svenpetersen1965/C64_PSU_Z66/Rev. 1/pictures/1055_-_DIN-Plug_top.JPG

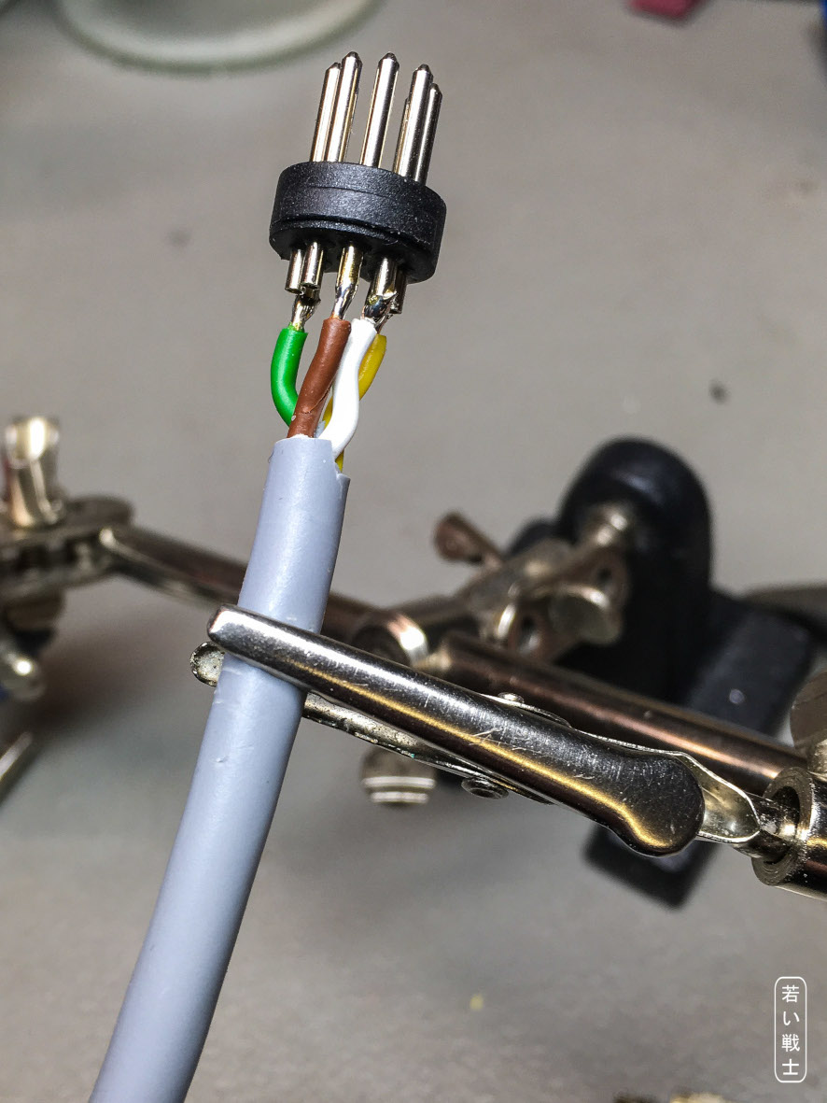
Rev. 1/pictures/1055_-_DIN-Plug_top.JPG
