svenpetersen1965/C64_PSU_Z66/Rev. 1/pictures/1056_-_DIN-Plug_bottom.JPG

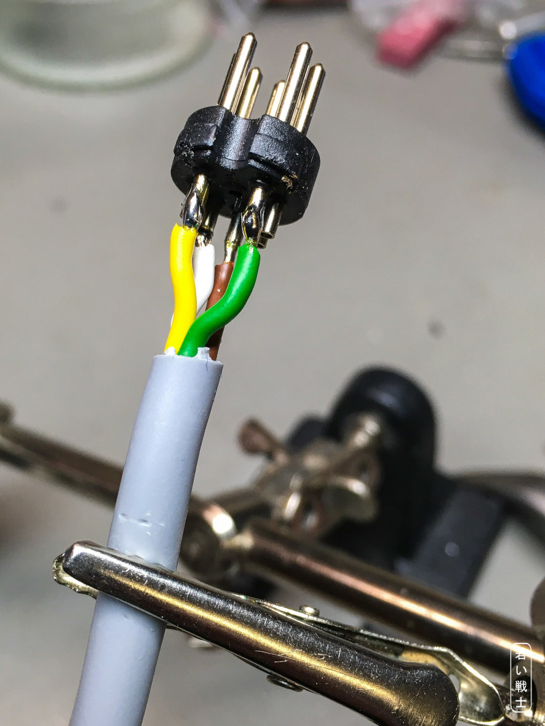
Rev. 1/pictures/1056_-_DIN-Plug_bottom.JPG
