svenpetersen1965/C64_PSU_Z66/Rev. 1/pictures/1057_-_Mains_Switch.JPG

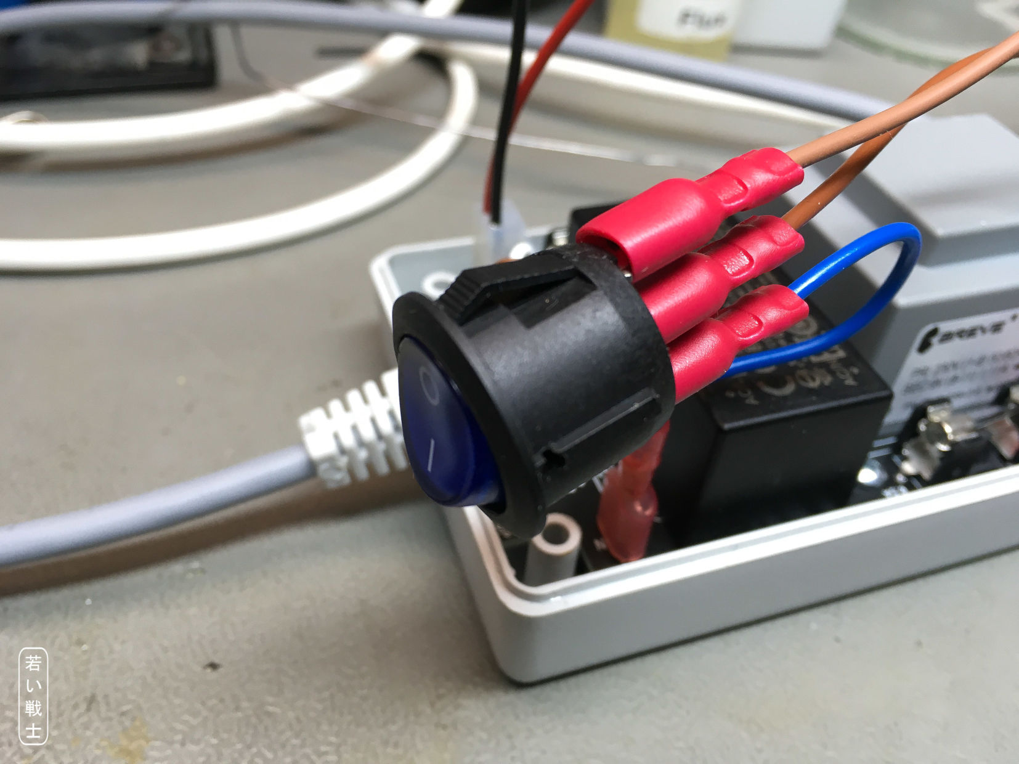
Rev. 1/pictures/1057_-_Mains_Switch.JPG
