svenpetersen1965/C64_PSU_Z66/Rev. 1/pictures/1165_-_thermal_el_load.JPG

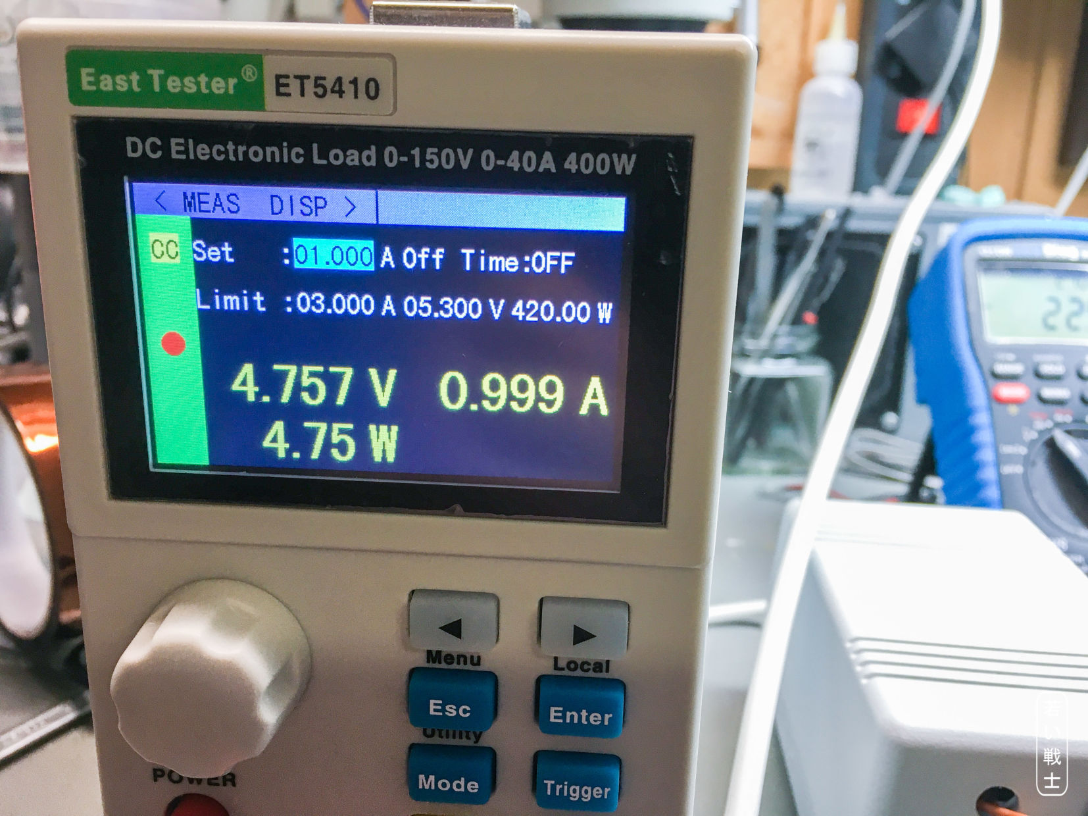
Rev. 1/pictures/1165_-_thermal_el_load.JPG
