svenpetersen1965/C64_PSU_Z66/Rev. 1/pictures/1166_-_thermal_load_resistors.JPG

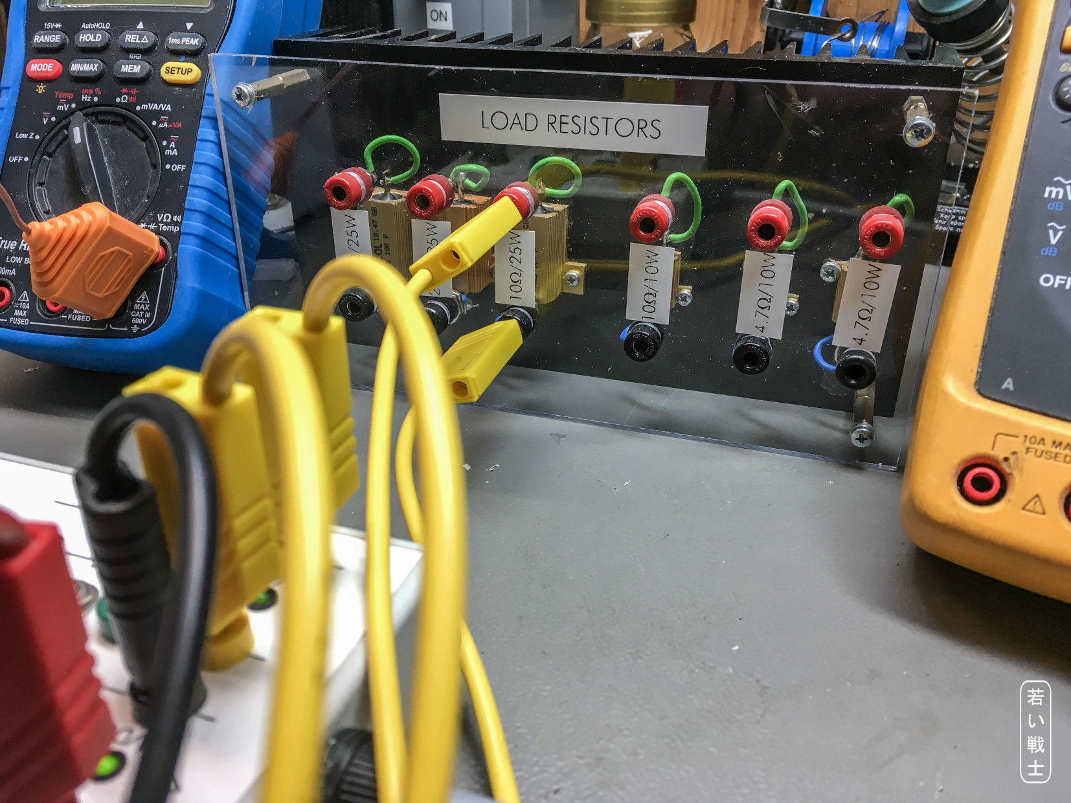
Rev. 1/pictures/1166_-_thermal_load_resistors.JPG
