svenpetersen1965/C64_PSU_Z66/Rev. 1/pictures/1183_-_thermal_final_config.JPG

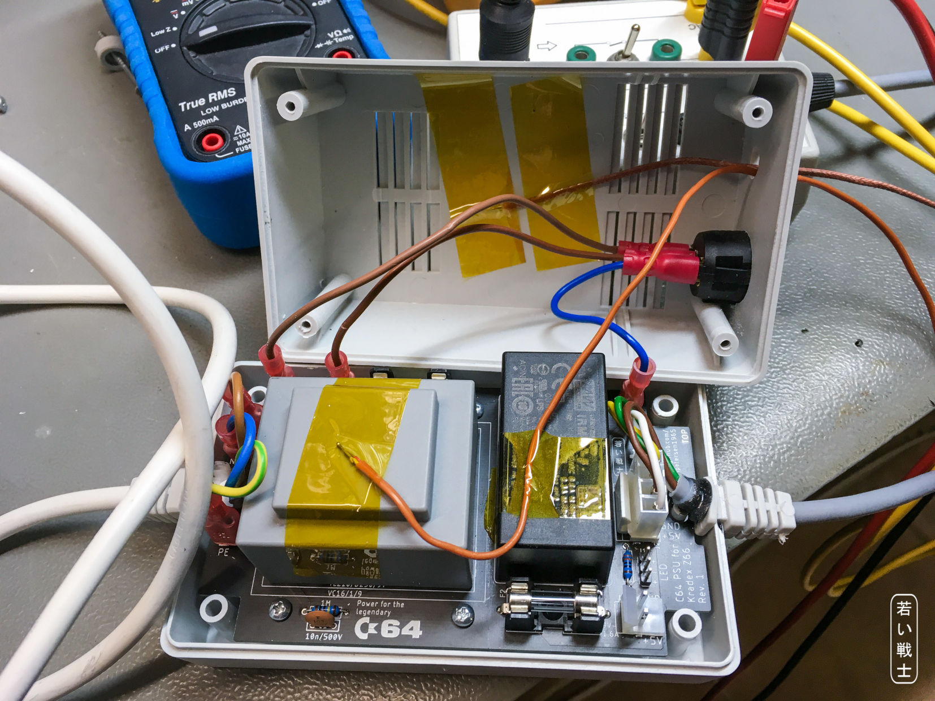
Rev. 1/pictures/1183_-_thermal_final_config.JPG
