svenpetersen1965/C64_PSU_Z66/Rev. 1/pictures/1190_-_thermal_final_start_condition_16VA.JPG

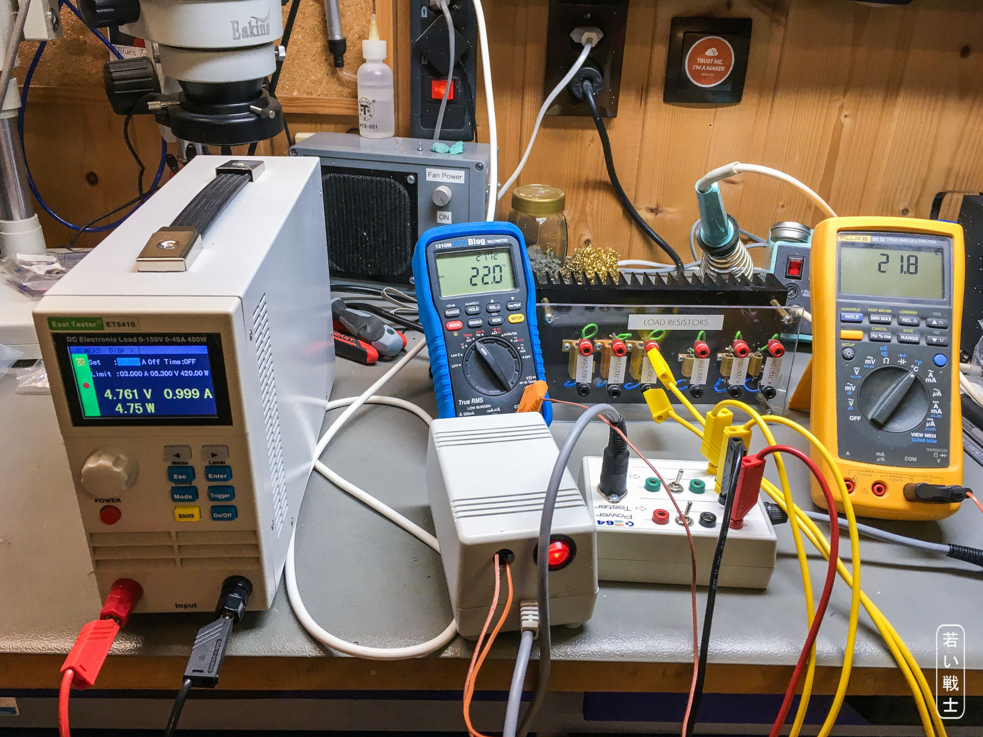
Rev. 1/pictures/1190_-_thermal_final_start_condition_16VA.JPG
