svenpetersen1965/C64_PSU_Z66/Rev. 1/pictures/1202_-_thermal_final_reading_16VA.JPG

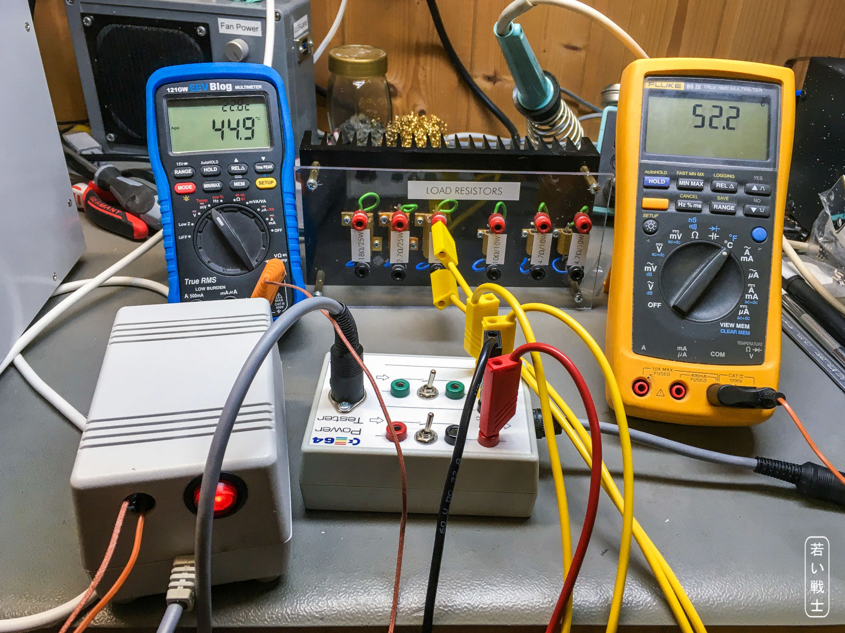
Rev. 1/pictures/1202_-_thermal_final_reading_16VA.JPG
