svenpetersen1965/C64_PSU_Z66/Rev. 1/pictures/20220217-194548.jpg

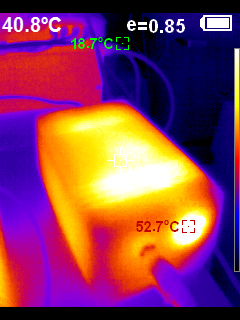
Rev. 1/pictures/20220217-194548.jpg
