svenpetersen1965/C64_PSU_Z66/Rev. 1/pictures/20220217-210124_FLIR_inside_9h.jpg

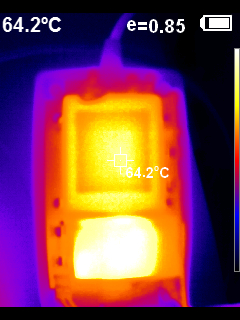
Rev. 1/pictures/20220217-210124_FLIR_inside_9h.jpg
