svenpetersen1965/C64_PSU_Z66/Rev. 1/pictures/FLIR_combi_9h.jpg

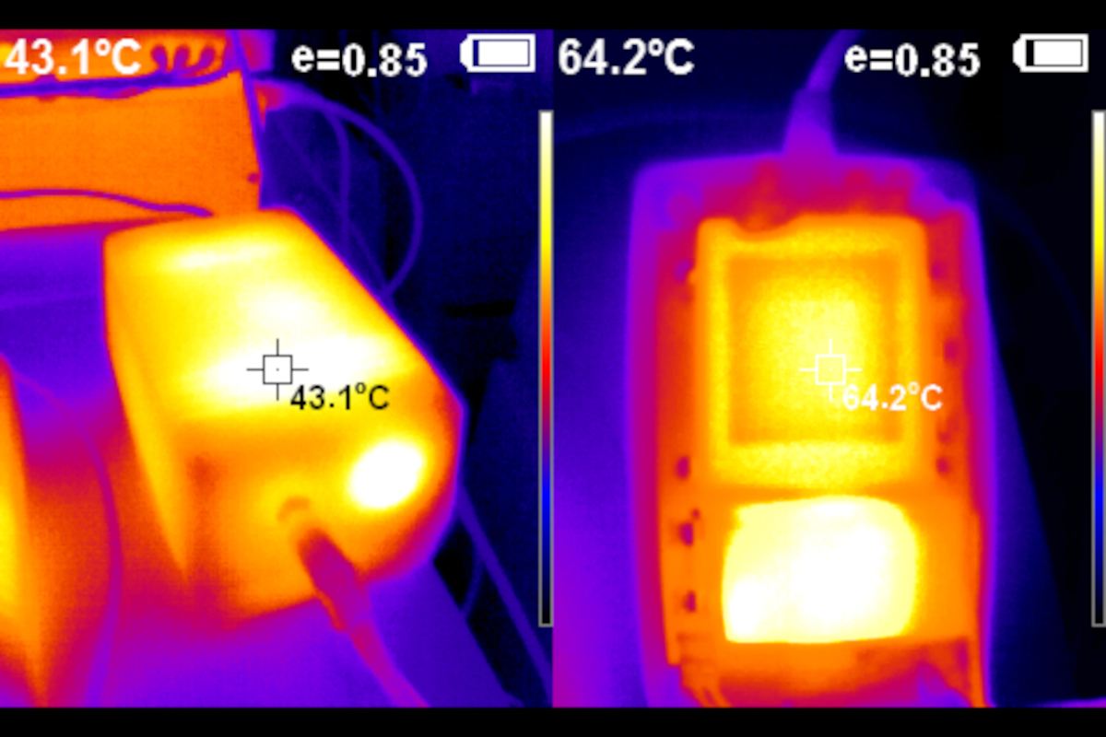
Rev. 1/pictures/FLIR_combi_9h.jpg
