svenpetersen1965/C64_PSU_Z66/Rev. 1/pictures/IRM-5-20_ripple.png

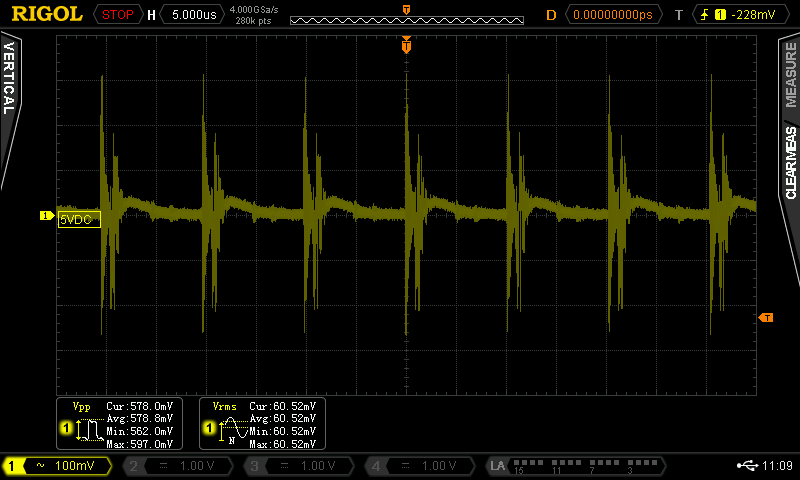
Rev. 1/pictures/IRM-5-20_ripple.png
