svenpetersen1965/C64_PSU_Z66/Rev. 1/pictures/MPM-10-5_ripple.png

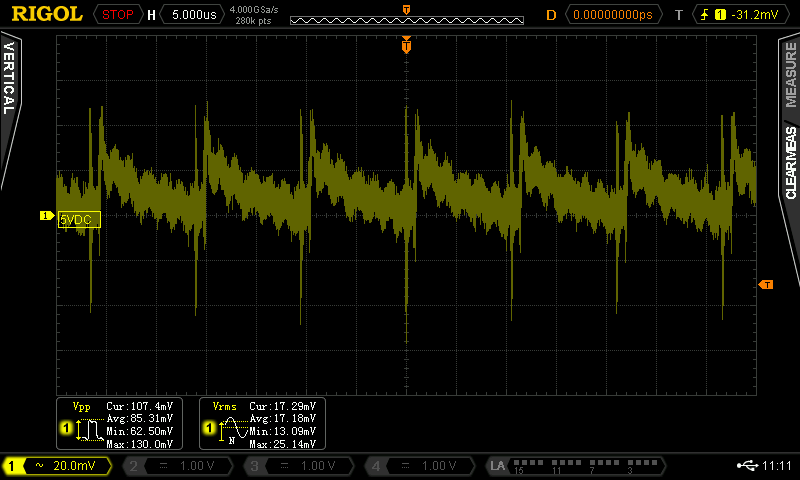
Rev. 1/pictures/MPM-10-5_ripple.png
